FSEI-Rgbg/FSEI-LED_Wuerfel/Bilder/v2.0/Render_JLCPCB-Gerber_Back.png

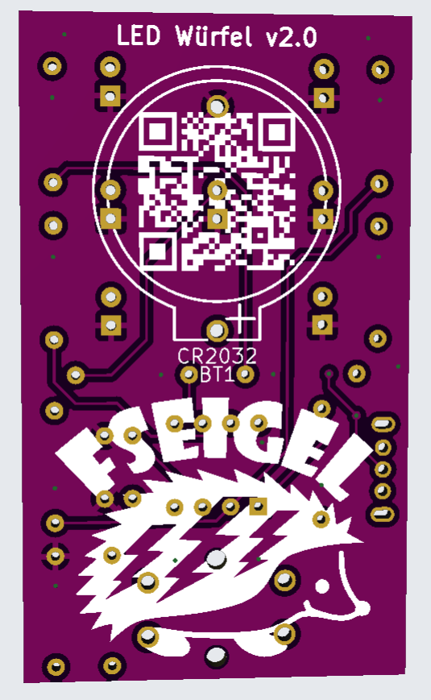
Bilder/v2.0/Render_JLCPCB-Gerber_Back.png
