FSEI-Rgbg/FSEI-LED_Wuerfel/Bilder/v2.0/Render_JLCPCB-Gerber_Front.png

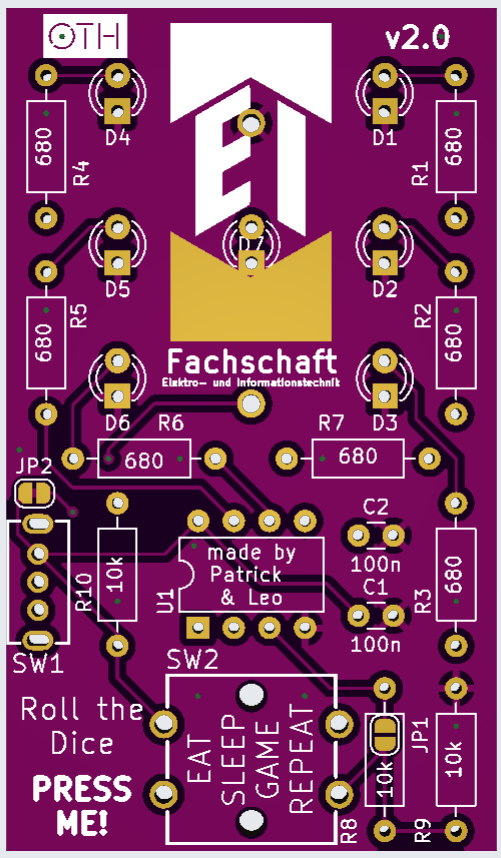
Bilder/v2.0/Render_JLCPCB-Gerber_Front.png
