FSEI-Rgbg/FSEI-LED_Wuerfel/Bilder/v2.0/Render_KiCAD_Back_Populated.png

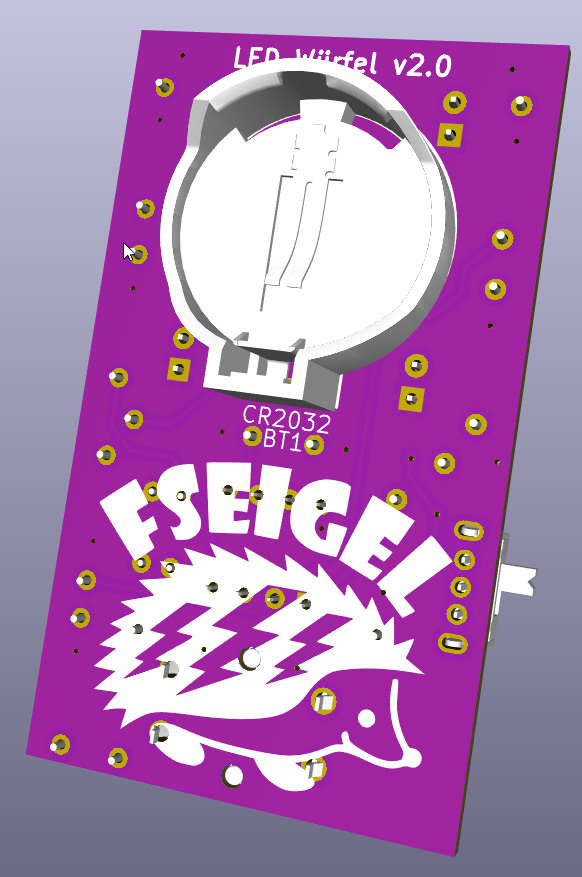
Bilder/v2.0/Render_KiCAD_Back_Populated.png
