FSEI-Rgbg/FSEI-LED_Wuerfel/Bilder/v2.0/Render_KiCAD_Front.png

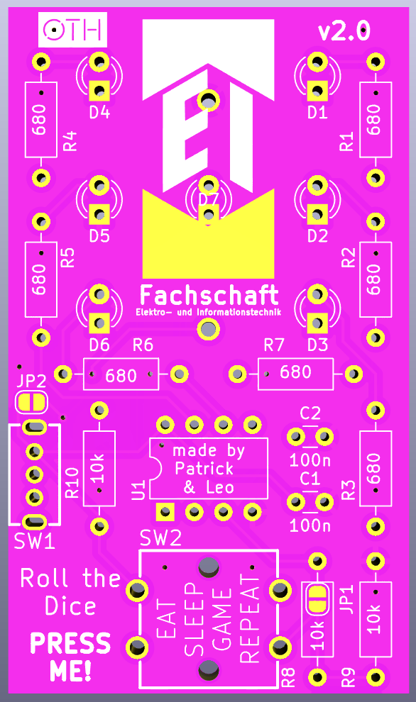
Bilder/v2.0/Render_KiCAD_Front.png
